tyllmoritz/ESPuino/PCBs/Kicad-Files/Headphone with PCM5102a and TDA1308/Kicad/KopfhoAÌaÌrerbuchse mit PCM5102A.sch

## KiCad design PCBs/Kicad-Files/Headphone with PCM5102a and TDA1308/Kicad/KopfhoAÌaÌrerbuchse mit PCM5102A.sch (2021-02-13)


Parts:
C1, C8, C9: 100µ; CP_Radial_D6.3mm_P2.50mm
C2, C12, C14, C16, C17: 100n; C_0603_1608Metric_Pad1.05x0.95mm_HandSolder
C3, C4: 1µ; C_0603_1608Metric_Pad1.05x0.95mm_HandSolder
C5: 22µ; CP_Radial_D4.0mm_P1.50mm
C10, C11: 2,2n; C_0603_1608Metric_Pad1.05x0.95mm_HandSolder
C13, C15: 2,2µ; C_0603_1608Metric_Pad1.05x0.95mm_HandSolder
H1, H2: MountingHole; MountingHole_3.2mm_M3
J1: Conn_02x03_Odd_Even; PinHeader_2x03_P2.54mm_Vertical_large
J2: AudioJack3_Dual_Switch; Jack_3.5mm_Cliff_Horizontal
Q1: IRLML6401; SOT-23
R2, R3, R5, R12: 10k; R_0805_2012Metric_Pad1.15x1.40mm_HandSolder
R4: 100k; R_0805_2012Metric_Pad1.15x1.40mm_HandSolder
R6, R7, R8, R9: 3,9k; R_0805_2012Metric_Pad1.15x1.40mm_HandSolder
R10, R11, R13, R14, R15: 470; R_0805_2012Metric_Pad1.15x1.40mm_HandSolder
U1: PCM5102A; TSSOP-20_4.4x6.5mm_P0.65mm
U2: TDA1308; SO-8_5.3x6.2mm_P1.27mm

Connections:
3,3V: C1.1, C2.1, C12.1, C14.1, C16.1, J1.2, Q1.2 (S), R3.1, R4.2, R12.2, U1.1 (CPVDD), U1.8 (AVDD), U1.20 (DVDD), U2.8 (V+)
BCK: J1.3, R15.2
DIN: J1.1, R14.2
GND: C1.2, C2.2, C5.2, C10.2, C11.2, C12.2, C13.1, C14.2, C16.2, C17.1, J1.4, J2.1 (S1), R2.1, R5.2, U1.3 (CPGND), U1.9 (AGND), U1.10 (DEMP), U1.11 (FLT), U1.12 (SCK), U1.16 (FMT), U1.19 (DGND), U2.4 (VSS)
LCK: J1.5, R13.2
unnamed: C3.2, R6.1
unnamed: C4.2, R7.1
unnamed: C5.1, R3.2, R5.1, U2.3 (+), U2.5 (+)
unnamed: C8.1, R8.2, U2.1
unnamed: C8.2, J2.5 (T1)
unnamed: C9.1, R9.2, U2.7
unnamed: C9.2, J2.3 (R1)
unnamed: C13.2, U1.5 (VNEG)
unnamed: C15.1, U1.4 (CAPM)
unnamed: C15.2, U1.2 (CAPP)
unnamed: C17.2, U1.18 (LDOO)
unnamed: J1.6, Q1.3 (D), R2.2
unnamed: J2.2 (SN1), Q1.1 (G), R4.1
unnamed: R6.2, R8.1, U2.2 (-)
unnamed: R7.2, R9.1, U2.6 (-)
unnamed: R10.2, U1.6 (OUTL)
unnamed: R11.2, U1.7 (OUTR)
unnamed: R12.1, U1.17 (XSMT)
unnamed: R13.1, U1.15 (LRCK)
unnamed: R14.1, U1.14 (DIN)
unnamed: R15.1, U1.13 (BCK)
OUTL: C3.1, C10.1, R10.1
OUTR: C4.1, C11.1, R11.1
